bklaric1/feather_esp_32_s3_mainboard/models/693071020811_rev1.stp

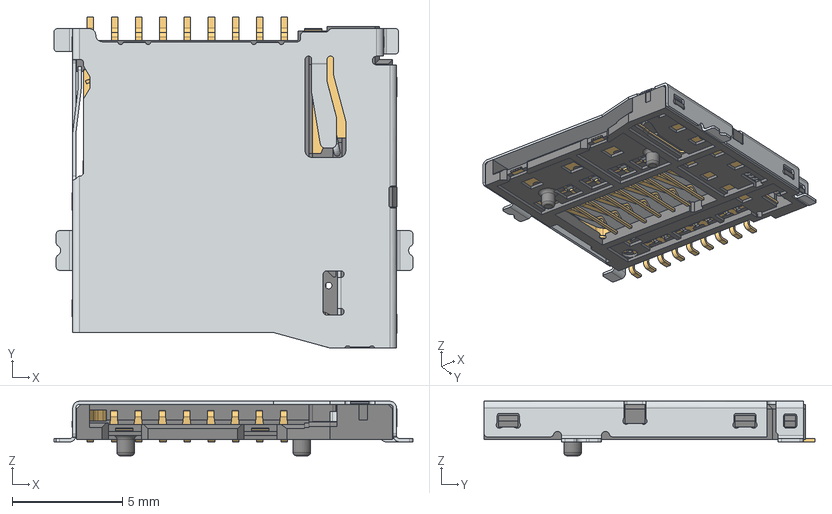
[picture p16: CAD file, 2024-10-20]
models/693071020811_rev1.stp
16.3 x 15.0 x 2.48 mm
693071020811_Housing
693071020811_Guide
693071020811_Spring
693071020811_Contact
693071020811_Hook
693071020811_Agraphe
693071020811_Shielding
