bklaric1/feather_esp_32_s3_mainboard/models/450405020524.step

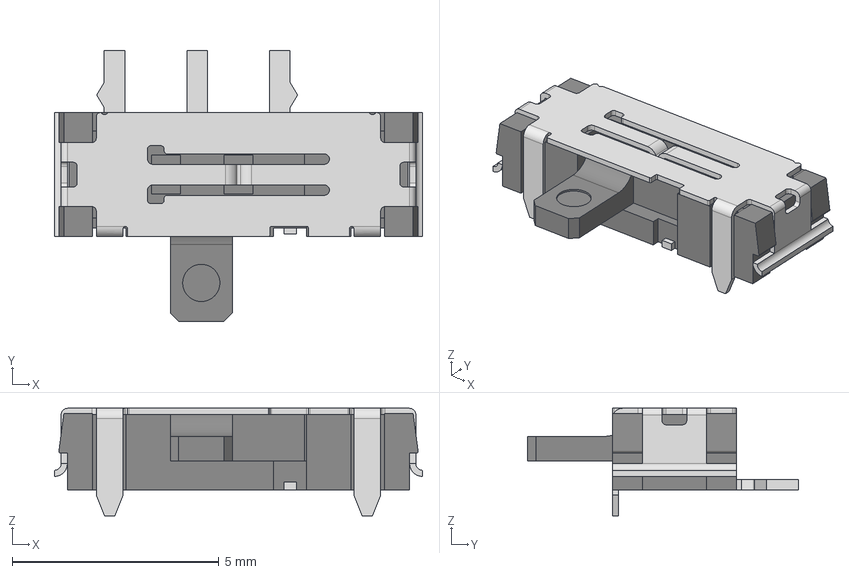
[picture p17: CAD file, 2024-10-19]
models/450405020524.step
8.90 x 6.55 x 2.60 mm
Frame
Cover
Pin 2
Pin 4
Slider 1
Pin 1
Pin 3
Slider
Pin 5
