bklaric1/feather_esp_32_s3_mainboard/models/744773033-56544.step

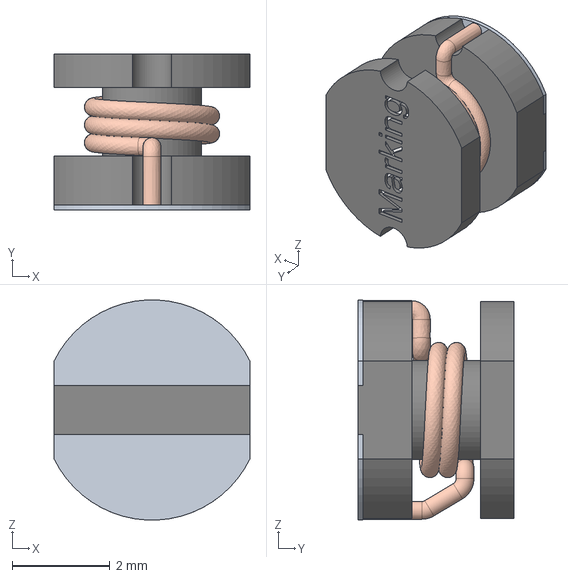
[picture p18: CAD file, 2024-10-16]
models/744773033-56544.step
4.00 x 3.18 x 4.49 mm
