bklaric1/feather_esp_32_s3_mainboard/models/430182050816 (rev1).stp

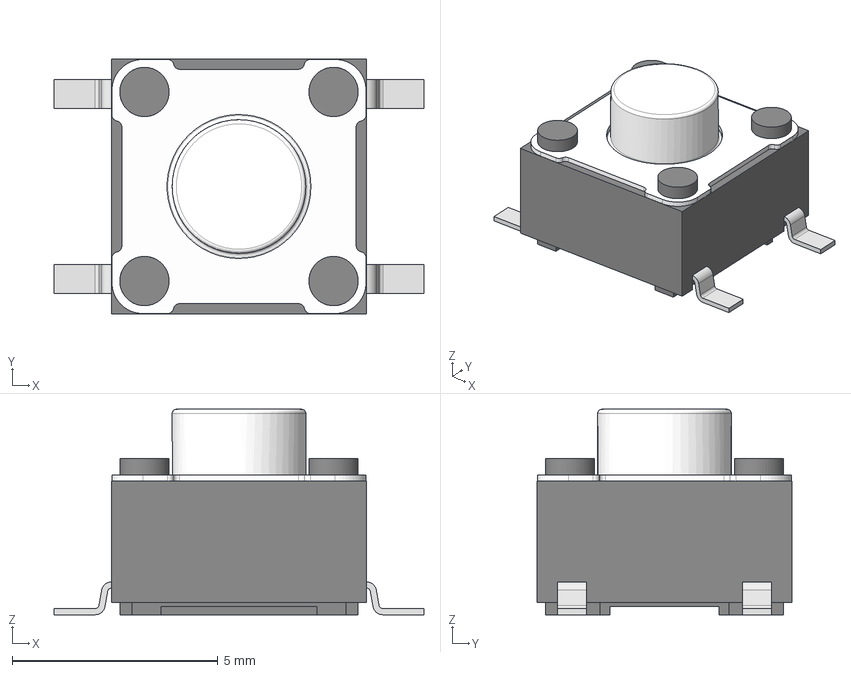
[picture p19: CAD file, 2024-10-16]
models/430182050816 (rev1).stp
9.00 x 6.20 x 5.00 mm
